nomanshahsyed/Nomi-s_Smart_Socket/Pictures/WIN_20191028_11_44_36_Pro.jpg

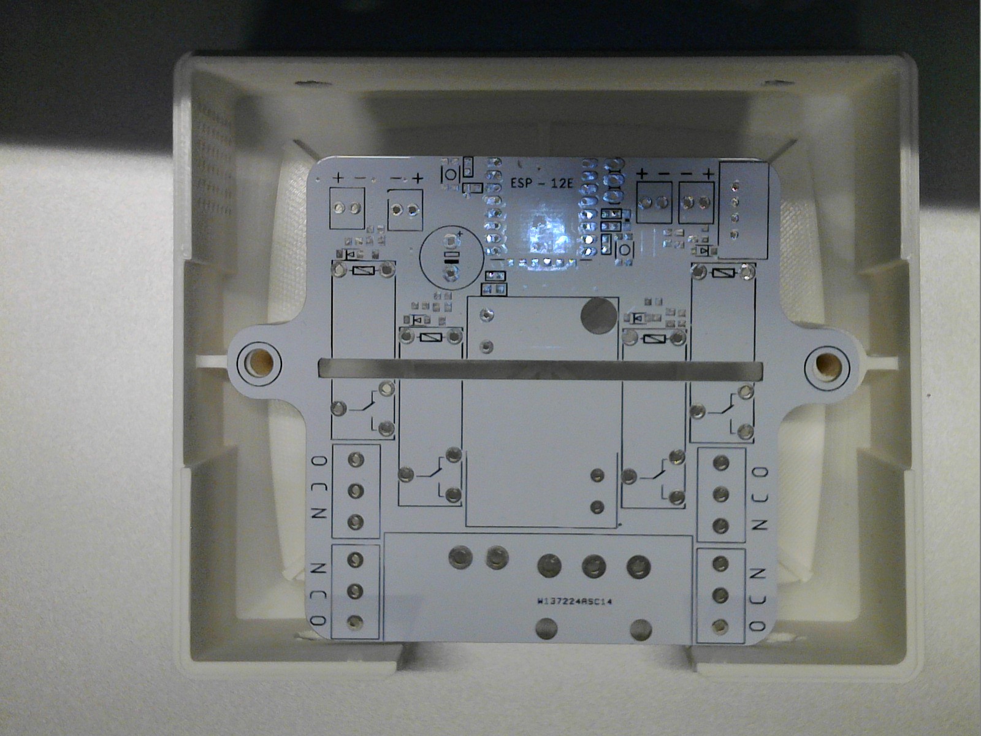
Pictures/WIN_20191028_11_44_36_Pro.jpg
