nomanshahsyed/Nomi-s_Smart_Socket/Pictures/WIN_20191028_11_49_31_Pro.jpg

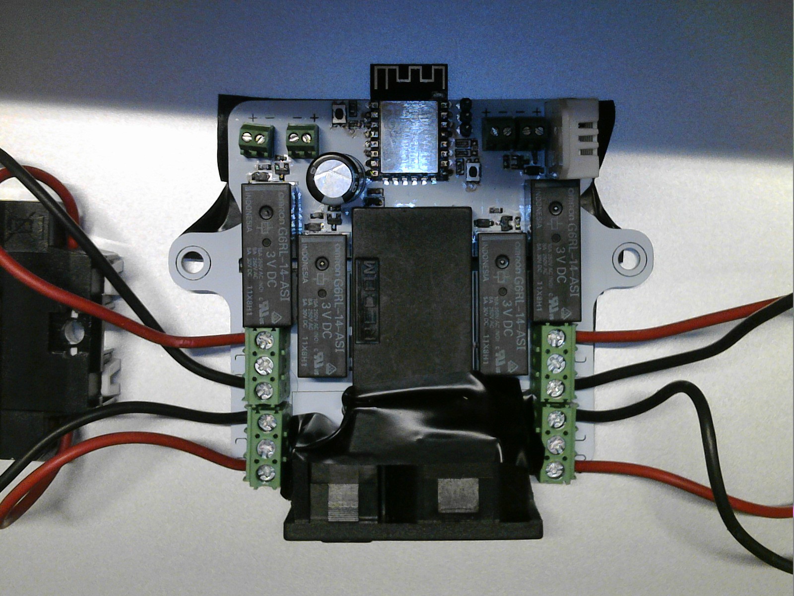
Pictures/WIN_20191028_11_49_31_Pro.jpg
